electrobob/led_logger_v3_git/Firmware/led_log/hw_init.c

/*
* board_init.c
*
* Created: 11/17/2013 19:04:59
*  Author: bogdan
*/
#ifdef __cplusplus
extern "C" {
	#endif
#include <asf.h>
#include "hw_init.h"
#include "cli.h"

void hw_init(void)
{
	
// 
// 	
// 	board_init();
// 	sysclk_init();
// 	rtc_init();
// 	//rtc_set_time(0);
// 	
// 	
// 	//Initiate the pins used
// 	
// 	ioport_init();
// 	
// 	ioport_set_pin_dir(MY_LED, IOPORT_DIR_OUTPUT);
// 	ioport_set_pin_dir(U_TX, IOPORT_DIR_OUTPUT);
// 	ioport_set_pin_dir(U_RX, IOPORT_DIR_INPUT);
// 	ioport_set_pin_level(MY_LED, 0);
// 
// 
// 
// 	//Initiate communication interfaces
// 	static usart_serial_options_t usart_options = {
// 		.baudrate = USART_SERIAL_BAUDRATE,
// 		.charlength = USART_SERIAL_CHAR_LENGTH,
// 		.paritytype = USART_SERIAL_PARITY,
// 		.stopbits = USART_SERIAL_STOP_BIT
// 	};
// 
// 	usart_serial_init(USART_SERIAL, &usart_options);
// 	
// 	


	
	
	
	
}

#ifdef __cplusplus
}
	#endif
