electrobob/led_logger_v3_git/Firmware/led_log/hw_init.h

/*
* board_init.h
*
* Created: 11/17/2013 19:03:18
*  Author: bogdan
*/
#ifdef __cplusplus
extern "C" {
	#endif

#ifndef BOARD_INIT_H_
#define BOARD_INIT_H_


// #define USART_SERIAL                     &USARTD0
// #define USART_SERIAL_BAUDRATE            115200
// #define USART_SERIAL_CHAR_LENGTH         USART_CHSIZE_8BIT_gc
// #define USART_SERIAL_PARITY              USART_PMODE_DISABLED_gc
// #define USART_SERIAL_STOP_BIT            false
// 
// #define MY_LED    IOPORT_CREATE_PIN(PORTE, 2)
// #define U_TX    IOPORT_CREATE_PIN(PORTD, 3)
// #define U_RX    IOPORT_CREATE_PIN(PORTD, 2)
// 
// #define ADC_PIN_V_MEASURE ADCCH_POS_PIN7
// #define ADC_PIN_I_MEASURE ADCCH_POS_PIN1
// 
// 
// 
// void hw_init(void);



#endif /* BOARD_INIT_H_ */

#ifdef __cplusplus
}
	#endif
